Evancli/porsche-quad-gauge/Photos/01.jpg

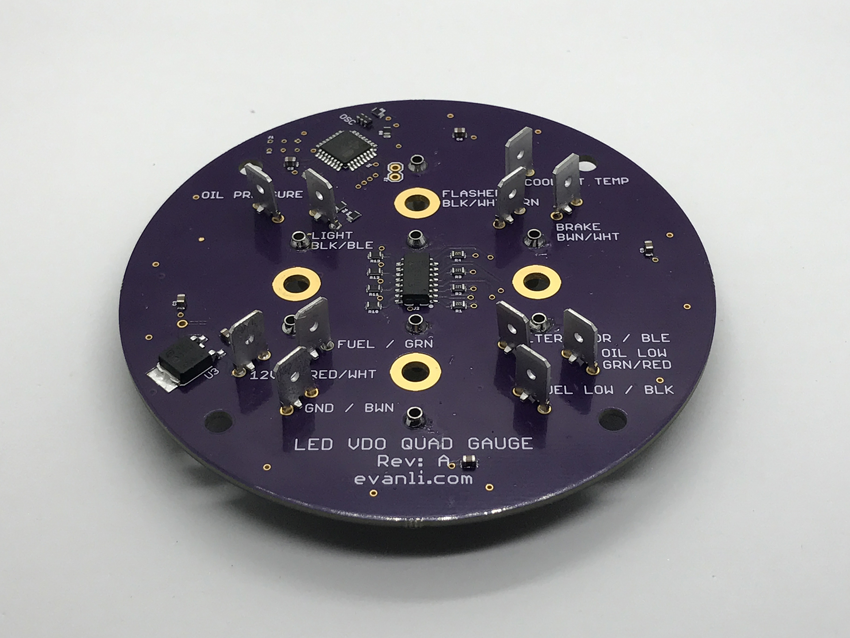
Photos/01.jpg
