Evancli/porsche-quad-gauge/Photos/02.jpg

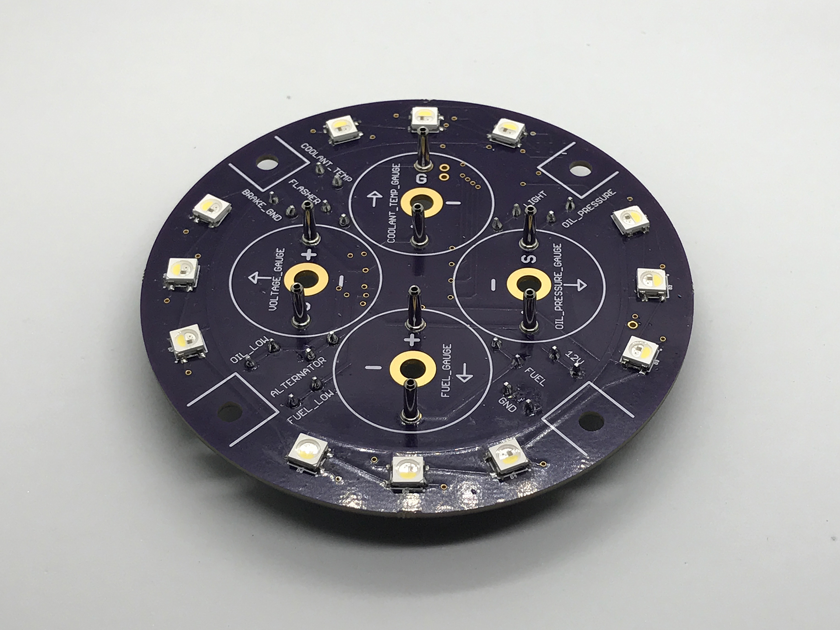
Photos/02.jpg
