Evancli/porsche-quad-gauge/Photos/03.jpg

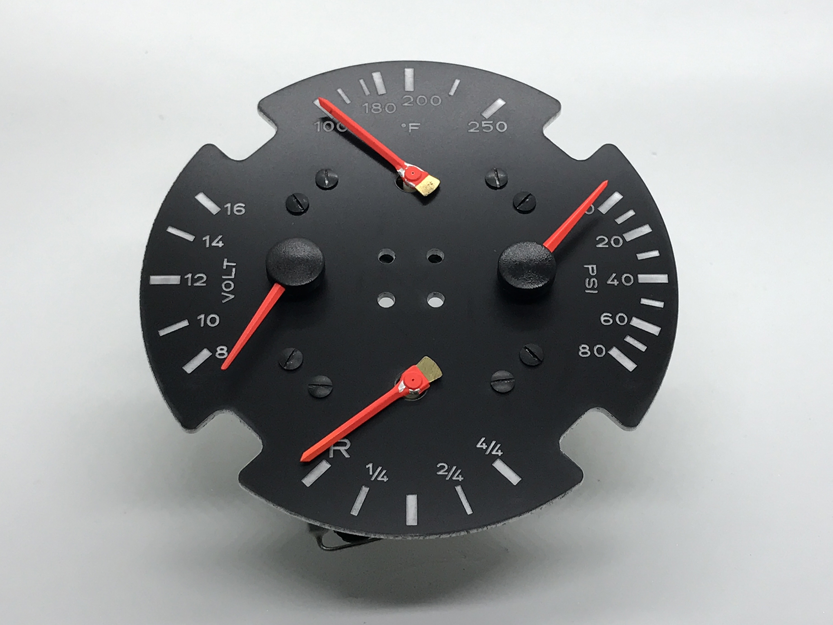
Photos/03.jpg
