Evancli/porsche-quad-gauge/Photos/04.jpg

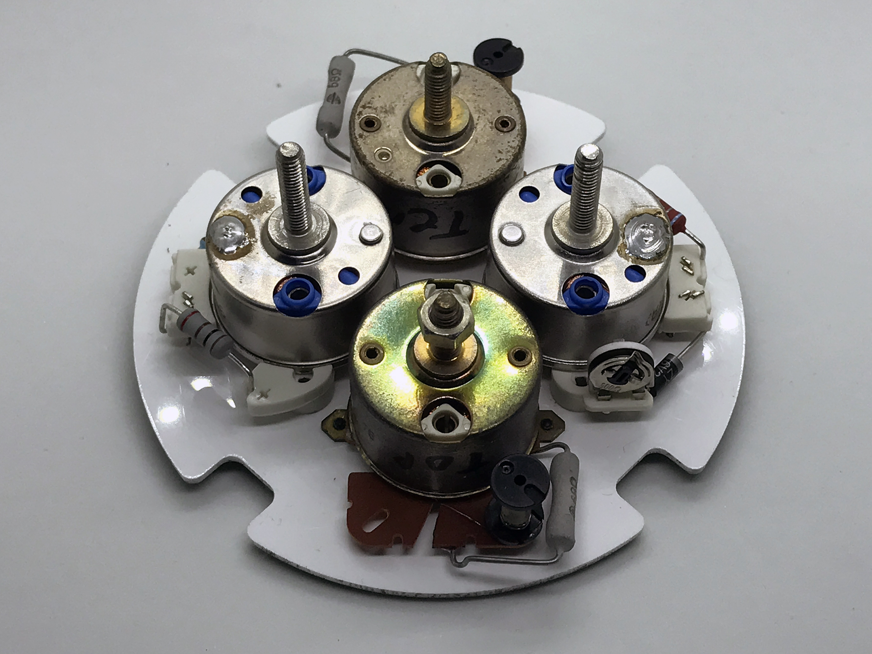
Photos/04.jpg
