Evancli/porsche-quad-gauge/Photos/05.jpg

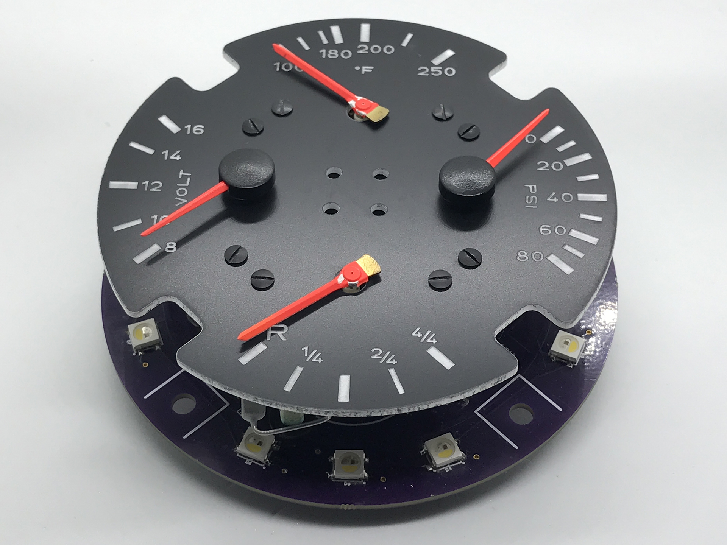
Photos/05.jpg
