Evancli/porsche-quad-gauge/Photos/06.jpg

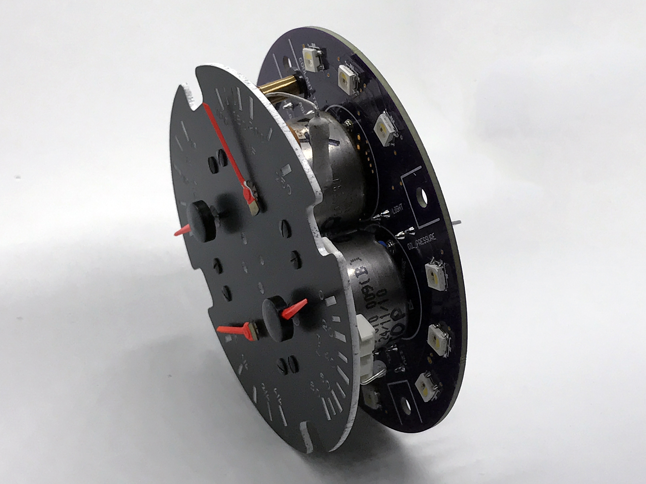
Photos/06.jpg
