Evancli/porsche-quad-gauge/Photos/07.jpg

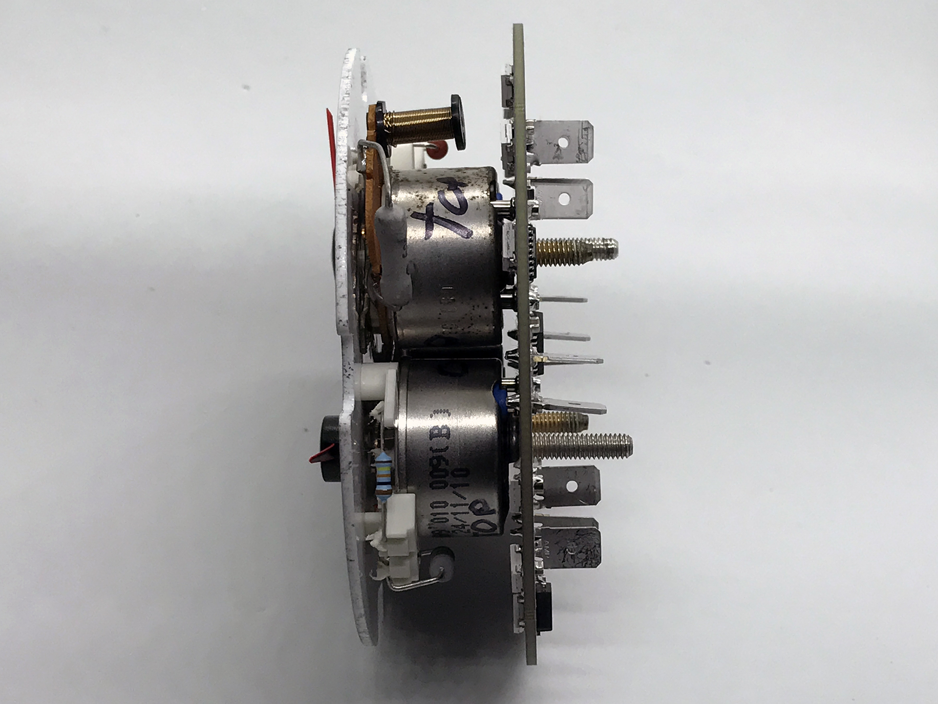
Photos/07.jpg
