Evancli/porsche-quad-gauge/Photos/08.jpg

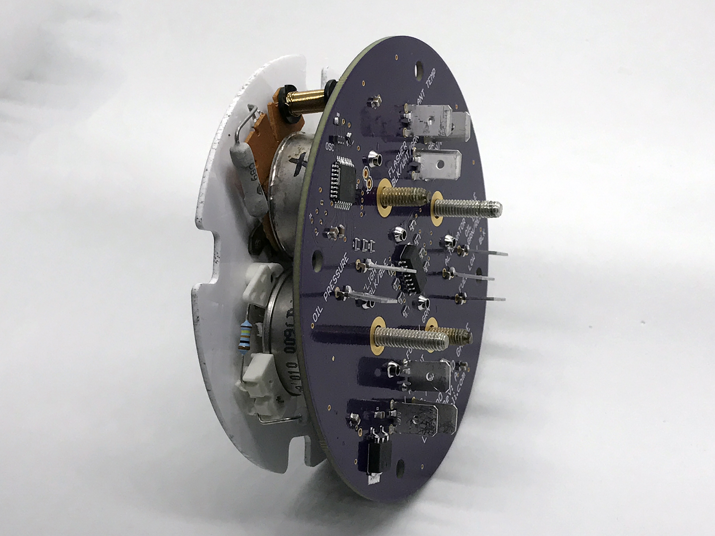
Photos/08.jpg
