Evancli/porsche-quad-gauge/Photos/09.jpg

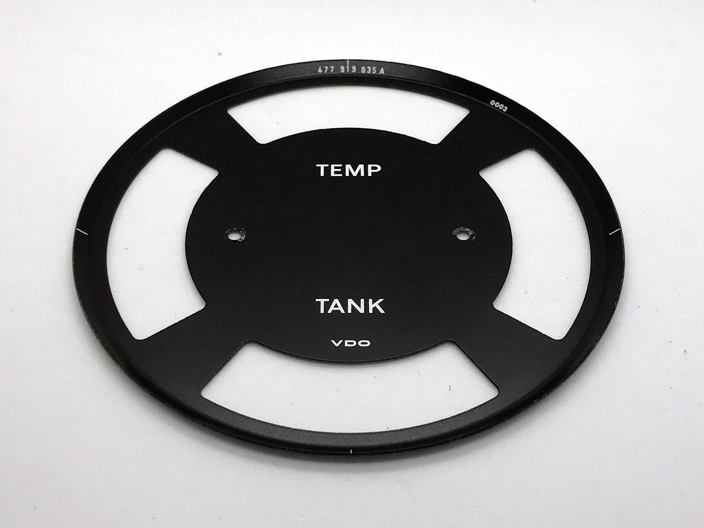
Photos/09.jpg
