Evancli/porsche-quad-gauge/Photos/10.jpg

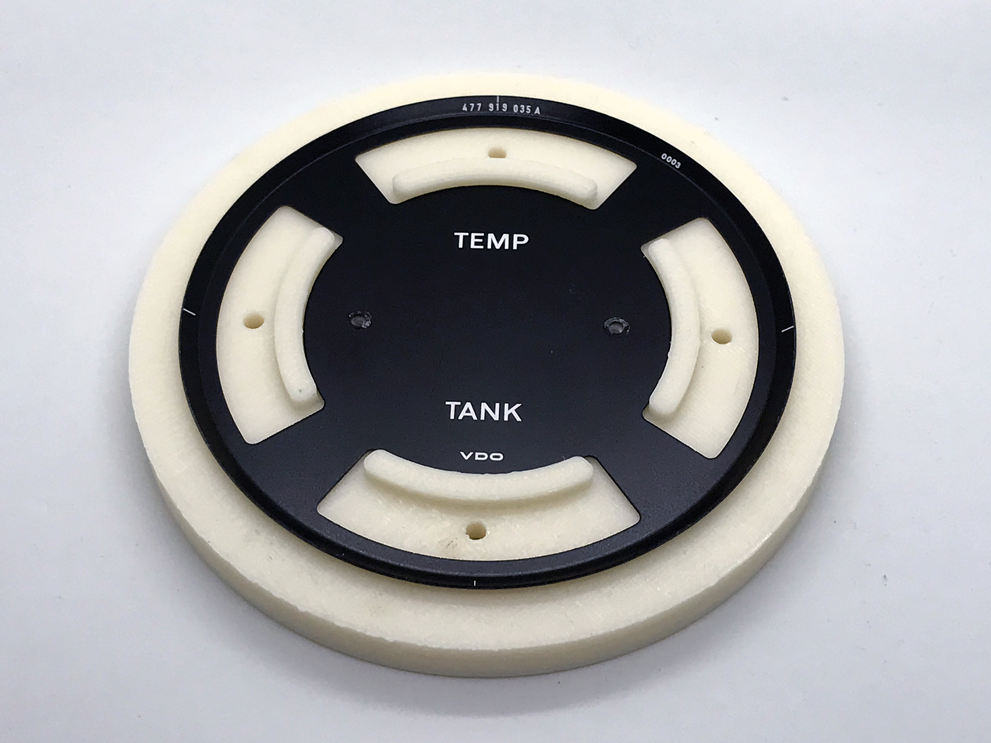
Photos/10.jpg
