Evancli/porsche-quad-gauge/Photos/11.jpg

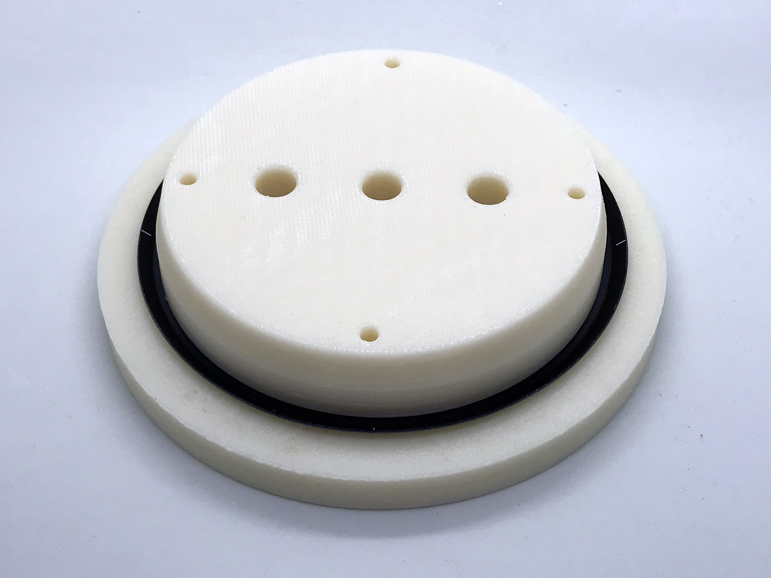
Photos/11.jpg
