Evancli/porsche-quad-gauge/Photos/12.jpg

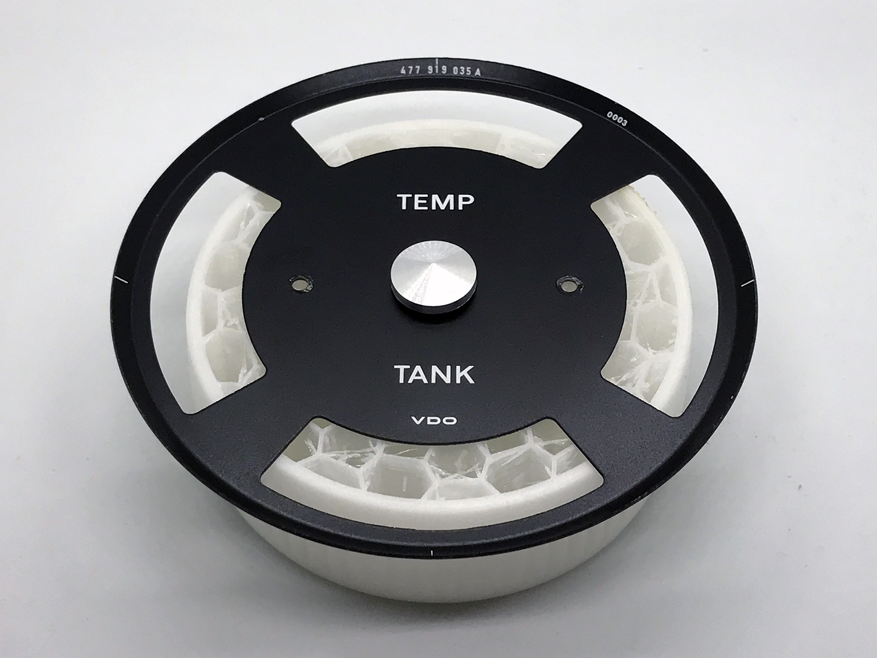
Photos/12.jpg
