Evancli/porsche-quad-gauge/Photos/13.jpg

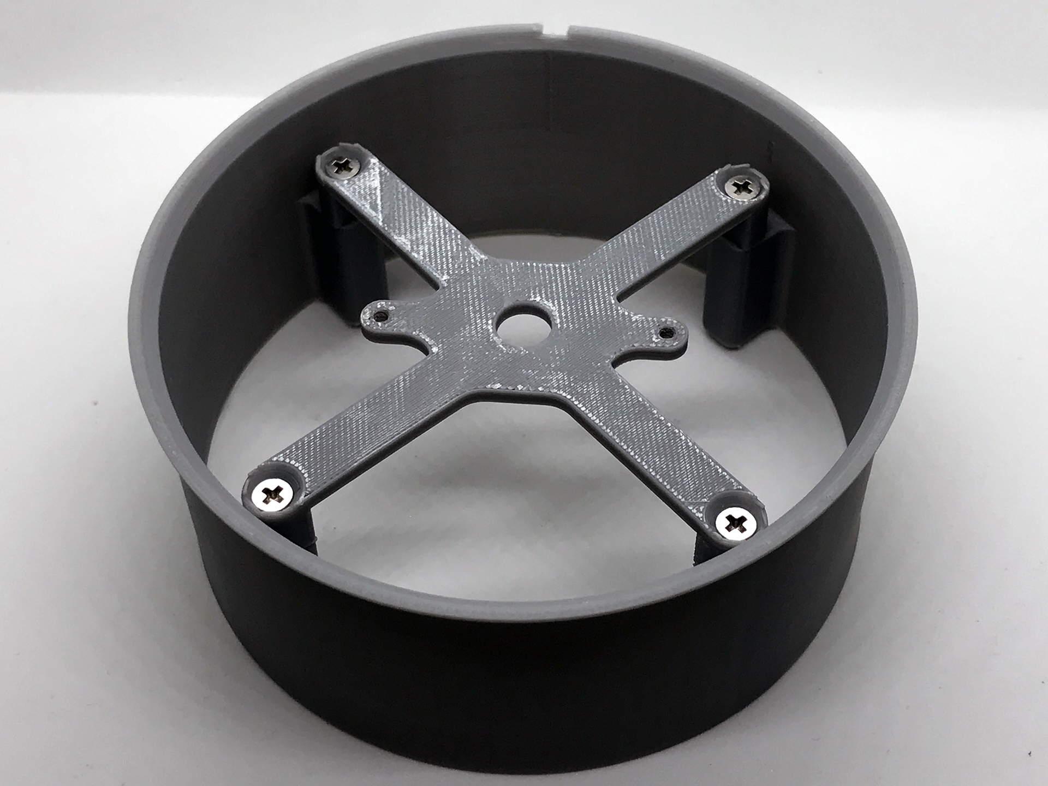
Photos/13.jpg
