Evancli/porsche-quad-gauge/Photos/14.jpg

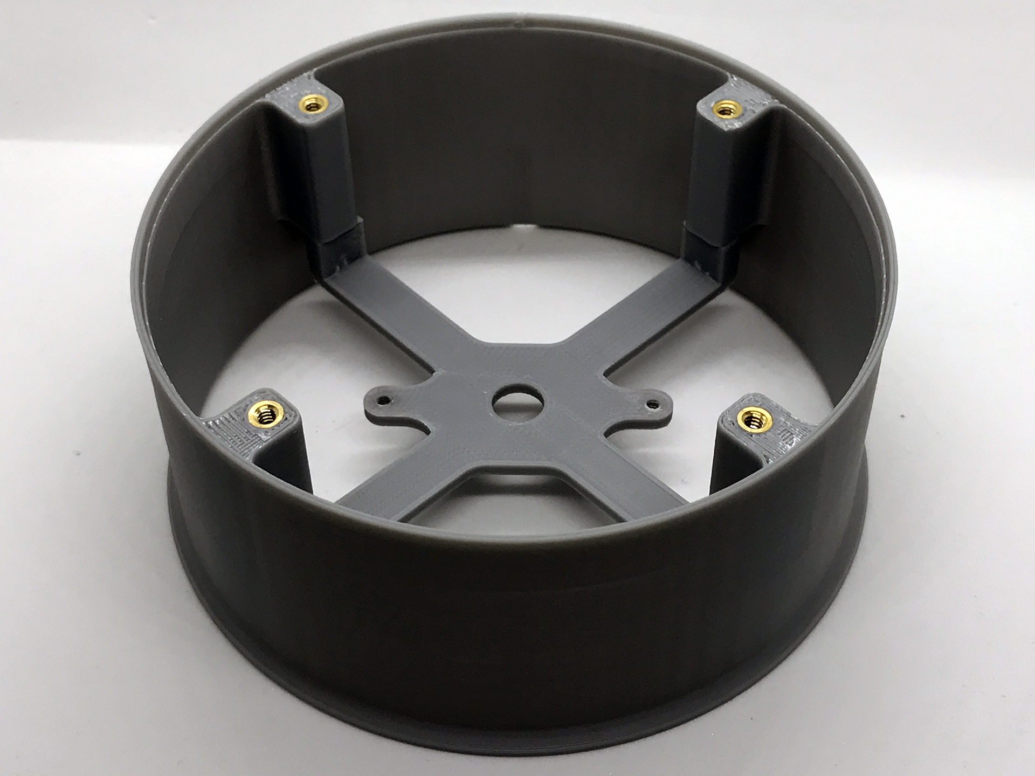
Photos/14.jpg
