Evancli/porsche-quad-gauge/Photos/15.jpg

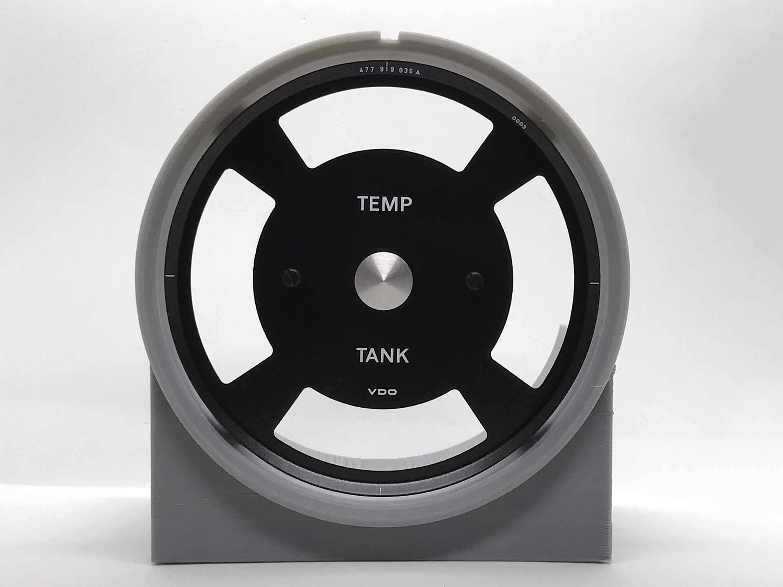
Photos/15.jpg
