Evancli/porsche-quad-gauge/Photos/16.jpg

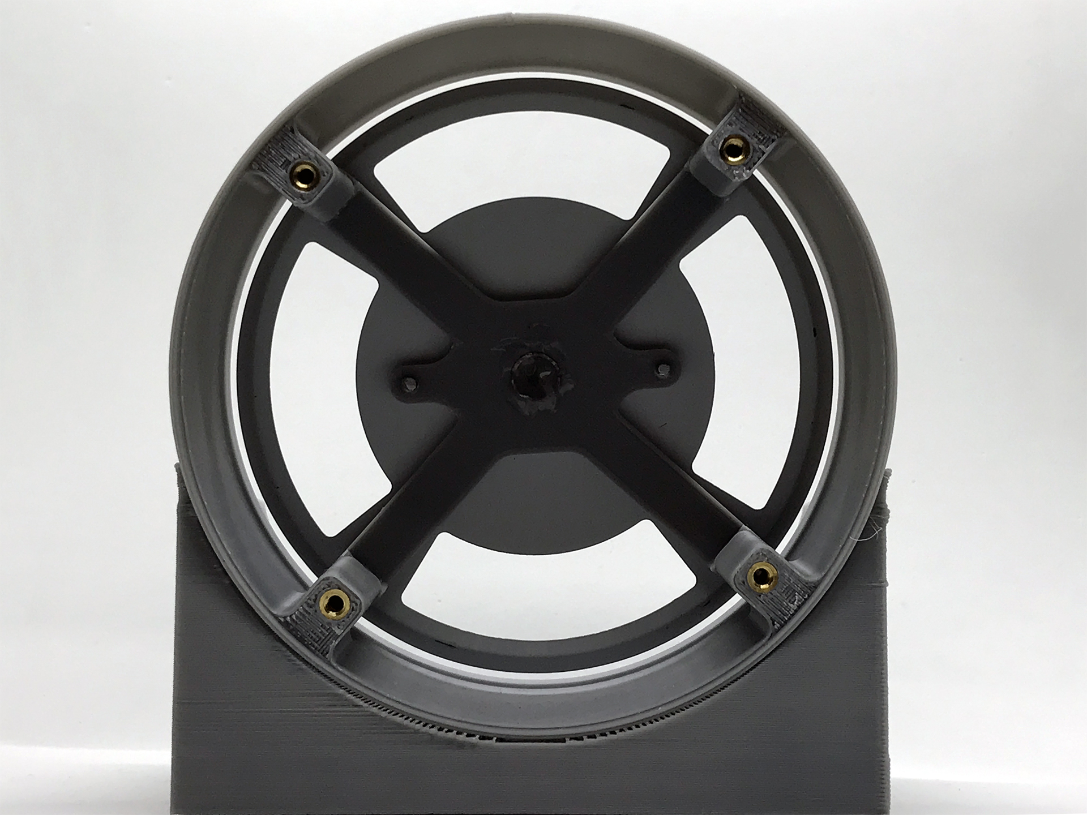
Photos/16.jpg
