Evancli/porsche-quad-gauge/Photos/17.jpg

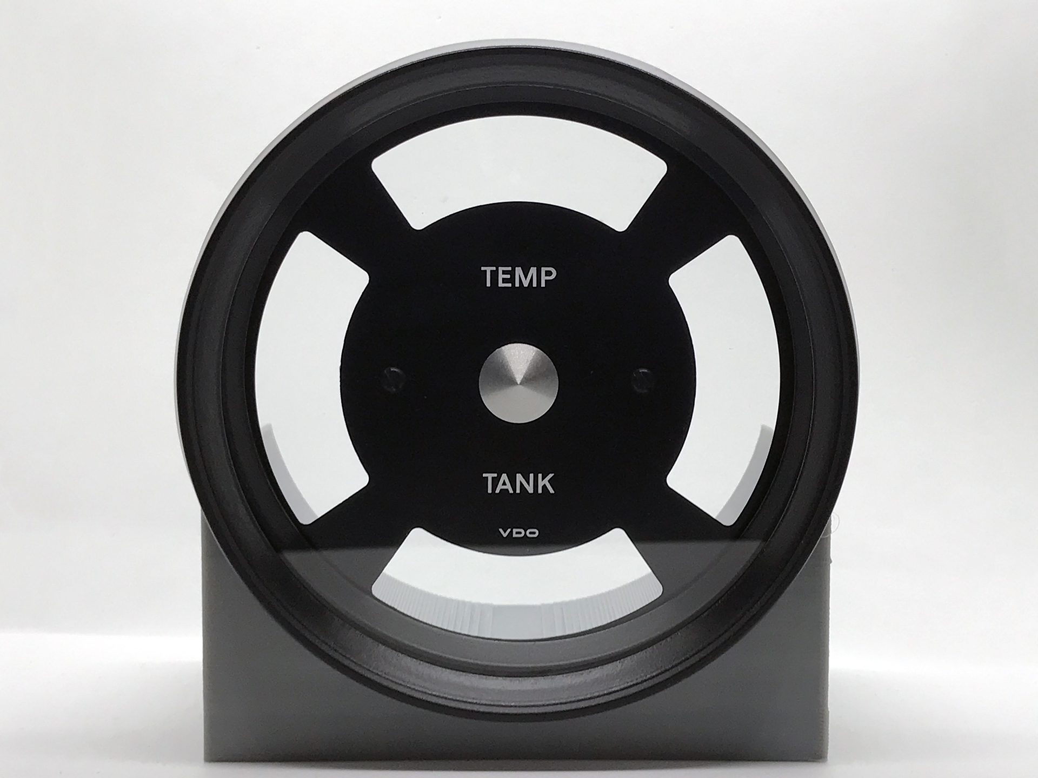
Photos/17.jpg
