Evancli/porsche-quad-gauge/Photos/18.jpg

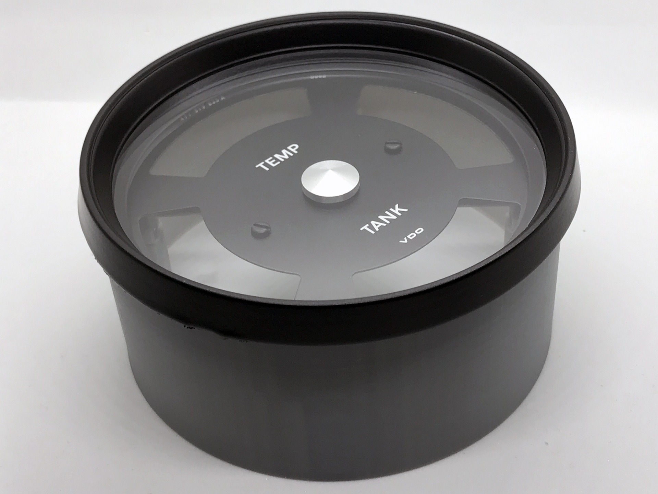
Photos/18.jpg
