Evancli/porsche-quad-gauge/Photos/20.jpg

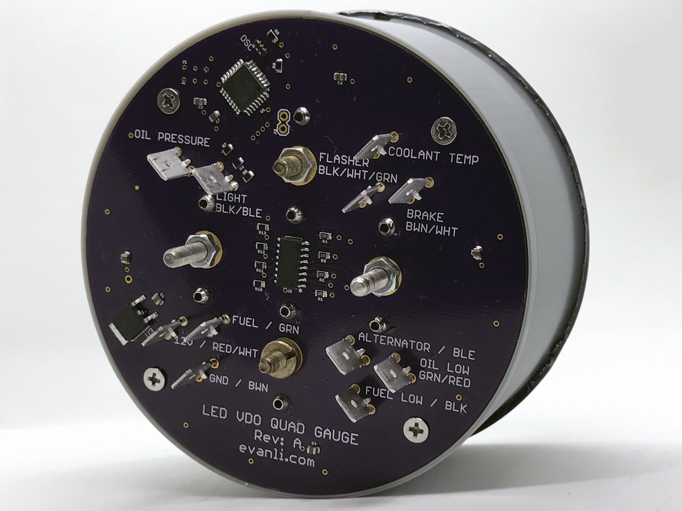
Photos/20.jpg
